MrWhite1878/AnalogEQ-Project/Simulation/Bell/bell.asc

C3: cap; 10n
C4: cap; 47n
R13: res; 2.2k
R14: res; 2.2k
R15: res; 4.7k
R16: res; 4.7k
R17: res; 12k
R18: res; 6.8k
R19: res; 6.8k
R20: res; 4.7k
R21: res; 4.7k
R22: res; 470
R23: res; 1k
R24: res; 12k
R25: res; {RV_23_4}
R26: res; {RV_12_4}
R27: res; {RV_12_6}
R28: res; {RV_23_6}
R29: res; {RV_12_7}
R30: res; {RV_23_7}
R31: res; {RV_12_7}
R32: res; {RV_23_7}
U5: TL072
U6: TL072
U7: TL072
U8: TL072
V1: voltage; ""; AC 1
V2: voltage; 18
V3: voltage; -18
Named nets: VS, 0, V+, V-, VM1
.ac oct 100 10 40k
.param Travel_4 = 0.2
.param R_Total_4 = 10k
.param TaperRatio_4 = table(Travel_4, 0,0, 0.1,0.05, 0.2,0.12, 0.3,0.22, 0.4,0.35, 0.5,0.5, 0.6,0.65, 0.7,0.78, 0.8,0.88, 0.9,0.95, 1,1)
.param RV_12_4 = {max(R_Total_4 * TaperRatio_4, 0.01 * R_Total_4)}
.param RV_23_4 = {max(R_Total_4 * (1 - TaperRatio_4), 0.01 * R_Total_4)}
.param Travel_6  = 0.5
.param R_Total_6 = 100k
.param TaperRatio_6 = table(Travel_6,  0,0, 0.1,0.05, 0.2,0.12, 0.3,0.22, 0.4,0.35, 0.5,0.5, 0.6,0.65, 0.7,0.78, 0.8,0.88, 0.9,0.95, 1,1)
.param RV_12_6 = {max(R_Total_6 * TaperRatio_6, 0.01 * R_Total_6)}
.param RV_23_6 = {max(R_Total_6 * (1 - TaperRatio_6), 0.01 * R_Total_6)}
.step param Travel_7 0 1 0.1
.param R_Total_7 = 100k
.param TaperRatio_7 = table(Travel_7, 0,0, 0.1,0.18, 0.2,0.38, 0.3,0.58, 0.4,0.74, 0.5,0.85, 0.6,0.92, 0.7,0.96, 0.8,0.98, 0.9,0.99, 1,1)
.param RV_12_7 = {max(R_Total_7 * TaperRatio_7, 0.01 * R_Total_7)}
.param RV_23_7 = {max(R_Total_7 * (1 - TaperRatio_7), 0.01 * R_Total_7)}
PTD902-2215K-B103
PTD904-2015K-C104
PTD902-1015K-B104
