MrWhite1878/AnalogEQ-Project/Simulation/Bell/douxchamps_bell.asc

V1: voltage; ""; AC 1
V2: voltage; 15
V3: voltage; -15
Named nets: VIN, 0, V+, V-
.ac oct 100 10 100k
.param posQ =0.5
.param posF =0.5
.step param posA list 0 0.25 0.75 1
