MrWhite1878/AnalogEQ-Project/Simulation/Bell/param_eq.asc

C1: cap; 1µf
C2: cap; 1nf
C3: cap; 1nf
R1: res; 10k
R2: res; 10k
R3: res; 10k
R4: res; 1k
R5: res; 15k
R6: res; 100k
R7: res; 11k
R8: res; 10k
R9: res; 1k
R10: res; 15k
R11: res; 3.9k
R12: res; 1k
R13: res; 21k
R14: res; 21k
R15: res; 1k
R16: res; 3.9k
R17: res; 22k
R18: res; 22k
R19: res; {RFV}
R20: res; {RFG}
R21: res; 390
R22: res; 12k
R23: res; 1k
R24: res; 9k
R25: res; 390
R26: res; 12k
U1: LT1358
U2: LT1358
U3: LT1358
U4: LT1358
U6: LT1358
V1: voltage; 10
V2: voltage; 10
V3: voltage; SINE(0 0.225); AC .225 0
Named nets: 0, out, input, Vneg, Vplus
RADJ 100k
RADJ
RADJ
RADJ
RADJ
.ac dec 1000 1 100000
RADJ 100k
GAIN?
Q
FREQ
.param RFV = (10k * posF + 10)
.param RFG = (10020 - RFV)
.step param posF list 0 0.5 0.9 1
