MrWhite1878/AnalogEQ-Project/Simulation/CombinedControl/combined.asc

C1: cap; 1µ
C2: cap; 1µ
C3: cap; 1µ
C4: cap; 10n
C5: cap; 680p
C6: cap; 10n
C7: cap; 100n
C8: cap; 100n
C9: cap; 15n
C10: cap; 15n
C11: cap; 10n
C12: cap; 47n
C13: cap; 1n
C14: cap; 4.7n
C15: cap; 47n
C16: cap; 47n
C17: cap; 47n
R1: res; 51k
R2: res; 3k
R3: res; 7.5k
R4: res; 1.2k
R5: res; 1.1k
R6: res; 3.9k
R7: res; 2.7k
R8: res; 1.8k
R9: res; 1.8k
R10: res; 12k
R11: res; 1k
R12: res; 1k
R13: res; 1k
R14: res; 2.2k
R15: res; 2.2k
R16: res; 4.7k
R17: res; 4.7k
R18: res; 12k
R19: res; 6.8k
R20: res; 6.8k
R21: res; 4.7k
R22: res; 4.7k
R23: res; 470
R24: res; 1k
R25: res; 12k
R26: res; 2.2k
R27: res; 2.2k
R28: res; 4.7k
R29: res; 4.7k
R30: res; 12k
R31: res; 6.8k
R32: res; 6.8k
R33: res; 4.7k
R34: res; 4.7k
R35: res; 470
R36: res; 1k
R37: res; 12k
R38: res; 47
R39: res; {RV_12_2}
R40: res; {RV_23_2}
R41: res; {RV_12_3}
R42: res; {RV_23_3}
R43: res; {RV_23_4}
R44: res; {RV_12_4}
R45: res; {RV_12_6}
R46: res; {RV_23_6}
R47: res; {RV_23_5}
R48: res; {RV_12_5}
R49: res; {RV_12_8}
R50: res; {RV_23_8}
R51: res; {RV_12_7}
R52: res; {RV_23_7}
R53: res; {RV_12_7}
R54: res; {RV_23_7}
R55: res; {RV_12_9}
R56: res; {RV_23_9}
R57: res; {RV_12_9}
R58: res; {RV_23_9}
R59: res; 139k
R60: res; 1k
R61: res; 12k
R62: res; 100
R63: res; 10k
R64: res; {RV_23_1}
R65: res; {RV_12_1}
R66: res; 47
R67: res; 220
U1: NE5532
U2: NE5532
U3: TL072
U4: TL072
U5: TL072
U6: TL072
U7: TL072
U8: TL072
U9: TL072
U10: TL072
U11: TL072
U12: TL072
U13: TL072
U14: TL072
V1: voltage; SINE(0 1.5 1k); AC 1
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
.param RV_12_1 = {max(R_Total_1 * TaperRatio_1, 0.01 * R_Total_1)}
.param RV_23_1 = {max(R_Total_1 * (1 - TaperRatio_1), 0.01 * R_Total_1)}
PTD902-2015K-A103
PTD902-2015K-A103
PTD902-1015K-B104
PTD902-1015K-B104
.dc oct V1 0.1 50 100
