MrWhite1878/AnalogEQ-Project/Simulation/Notch/notch.asc

C4: cap; 47n
C5: cap; 47n
C6: cap; 47n
R3: res; 139k
R7: res; 1k
R8: res; 12k
R9: res; 100
R10: res; 10k
R11: res; {RV_23_1}
R12: res; {RV_12_1}
U1: TL072
V1: voltage; ""; AC 1
V2: voltage; 18
V3: voltage; -18
Named nets: VLP, 0, V+, V-, VN
.ac oct 10000 100 500
.step param Travel_1 0 1 0.1
.param R_Total_1 = 10k
.param TaperRatio_1 = table(Travel_1, 0,0, 0.1,0.015, 0.2,0.035, 0.3,0.06, 0.4,0.10, 0.5,0.15, 0.6,0.24, 0.7,0.36, 0.8,0.54, 0.9,0.78, 1,1)
.param RV_12_1 = {max(R_Total_1 * TaperRatio_1, 0.01 * R_Total_1)}
.param RV_23_1 = {max(R_Total_1 * (1 - TaperRatio_1), 0.01 * R_Total_1)}
PTD902-2015K-A103
PTD902-2015K-A103
.noise V(vn) V1 oct 10000 10 40k
