MrWhite1878/AnalogEQ-Project/Simulation/Power/acac_doubler.asc

C1: cap; 470µ; Rser=0.1
C2: cap; 470µ; Rser=0.1
C3: cap; 100n
C4: cap; 100n
C5: cap; 100µ; Rser=0.1
C6: cap; 100µ; Rser=0.1
C7: cap; 470µ; Rser=0.1
C8: cap; 470µ; Rser=0.1
C9: cap; 470µ
C10: cap; 470µ
C11: cap; 100n
C12: cap; 100n
C13: cap; 100µ
C14: cap; 100µ
C15: cap; 1000µ
C16: cap; 1000µ
C17: cap; 100n
C18: cap; 100n
C19: cap; 100µ
C20: cap; 100µ
C21: cap; 1000µ
C22: cap; 1000µ
D1: diode; 1N4007
D2: diode; 1N4007
D3: diode; 1N4007
D4: diode; 1N4007
D5: diode; 1N4007
D6: diode; 1N4007
D7: diode; 1N4007
D8: diode; 1N4007
D9: diode; 1N4007
D10: diode; 1N4007
RL3: res; 175
RL4: res; 175
U1: LM7818
U2: LM7918
U3: LM7818
U4: LM7918
U5: LM7818
U6: LM7918
V1: voltage; SINE(0 17 55); Rser=2
V2: voltage; SINE(0 22.6 55)
V3: voltage; SINE(0 12.73 55); Rser=2
Named nets: V+, V-, 0, VIN, V+2, V-2, VIN2, V+3, V-3, VIN3
.tran 1
Expects 12VAC... make sure components voltage rating and wall wart output are compatible
Third Supply
