MrWhite1878/AnalogEQ-Project/Simulation/Power/Draft1.asc

I1: current; SINE(0 7.0710678 60)
L1: ind; 16; Rser=0
L2: ind; 1; Rser=0
R1: res; 60
R2: res; 20
R3: res; 40
K1 L1 L2 1
.tran 0.1666666666666
