MrWhite1878/AnalogEQ-Project/Simulation/Shelving/shelves.asc

C1: cap; 100n
C2: cap; 100n
C3: cap; 15n
C4: cap; 15n
R1: res; 1.8k
R2: res; 1.8k
R3: res; 12k
R4: res; 1k
R5: res; 1k
R6: res; 1k
R7: res; {RV_12_2}
R8: res; {RV_23_2}
R9: res; {RV_12_3}
R10: res; {RV_23_3}
U1: NE5532
V1: voltage; ""; AC 1
V2: voltage; 18
V3: voltage; -18
Named nets: VN, 0, V+, V-, VS
.ac oct 100 10 40k
PTD902-2215K-B103
PTD902-2215K-B103
.step param Travel_2 0 1 0.5
.param R_Total_2 = 10k
.param TaperRatio_2 = table(Travel_2, 0,0, 0.1,0.05, 0.2,0.12, 0.3,0.22, 0.4,0.35, 0.5,0.5, 0.6,0.65, 0.7,0.78, 0.8,0.88, 0.9,0.95, 1,1)
.param RV_12_2 = {max(R_Total_2 * TaperRatio_2, 0.01 * R_Total_2)}
.param RV_23_2 = {max(R_Total_2 * (1 - TaperRatio_2), 0.01 * R_Total_2)}
.step param Travel_3 0 1 0.5
.param R_Total_3 = 10k
.param TaperRatio_3 = table(Travel_3, 0,0, 0.1,0.05, 0.2,0.12, 0.3,0.22, 0.4,0.35, 0.5,0.5, 0.6,0.65, 0.7,0.78, 0.8,0.88, 0.9,0.95, 1,1)
.param RV_12_3 = {max(R_Total_3 * TaperRatio_3, 0.01 * R_Total_3)}
.param RV_23_3 = {max(R_Total_3 * (1 - TaperRatio_3), 0.01 * R_Total_3)}
.noise V(vs) V1 oct 100 10 40k
