MrWhite1878/AnalogEQ-Project/Simulation/Power/pifilter.asc

C1: cap; 10µ; Rser=1
C2: cap; 10µ; Rser=1
C3: cap; 10µ; Rser=1
C4: cap; 10µ; Rser=1
L1: ind; 10µ; Rser=1
L2: ind; 10µ; Rser=1
V1: voltage; SINE(15 50m 100k); AC 1
V2: voltage; SINE(-15 50m 100k); AC 1
Named nets: VOUT+, VOUT-, 0
.tran 100u
.ac dec 100 1 1Meg
ferrite bead inductors
