MrWhite1878/AnalogEQ-Project/sim/CombinedControl/combined.asc

C1: cap; 1µ
C2: cap; 1µ
C3: cap; 1µ
C4: cap; 10n
C5: cap; 680p
C6: cap; 10n
C7: cap; 100n
C8: cap; 100n
C9: cap; 15n
C10: cap; 15n
C11: cap; 10n
C12: cap; 47n
C13: cap; 1n
C14: cap; 4.7n
C15: cap; 220n
C16: cap; 220n
C17: cap; 220n
R1: res; 51k
R2: res; 3k
R3: res; 7.5k
R4: res; 1.2k
R5: res; 1.1k
R6: res; 3.9k
R7: res; 2.7k
R8: res; 1.8k
R9: res; 1.8k
R10: res; 12k
R11: res; 1k
R12: res; 1k
R13: res; 1k
R14: res; 2.2k
R15: res; 2.2k
R16: res; 4.7k
R17: res; 4.7k
R18: res; 12k
R19: res; 6.8k
R20: res; 6.8k
R21: res; 4.7k
R22: res; 4.7k
R23: res; 470
R24: res; 1k
R25: res; 12k
R26: res; 2.2k
R27: res; 2.2k
R28: res; 4.7k
R29: res; 4.7k
R30: res; 12k
R31: res; 6.8k
R32: res; 6.8k
R33: res; 4.7k
R34: res; 4.7k
R35: res; 470
R36: res; 1k
R37: res; 12k
R38: res; 100k
R39: res; 39k
R40: res; 1k
R41: res; 12k
R42: res; 100
R43: res; 10k
RG1: res; {10k*(1-posb)+20}
RG2: res; {10k*(1-post)+20}
RG3: res; {100k*(1-posF)+20}
RG4: res; {100k*(1-posF)+20}
RG5: res; {100k*(1-posQ)+20}
RG6: res; {10k*(1-posA)+20}
RG7: res; {100k*(1-posF)+20}
RG8: res; {100k*(1-posF)+20}
RG9: res; {100k*(1-posQ)+20}
RG10: res; {10k*(1-posA)+20}
RG11: res; {10k*(1-posF)+20}
RV1: res; {10k*posb+20}
RV2: res; {10k*post+20}
RV3: res; {100k*posF+20}
RV4: res; {100k*posF+20}
RV5: res; {100k*posQ+20}
RV6: res; {10k*posA+20}
RV7: res; {100k*posF+20}
RV8: res; {100k*posF+20}
RV9: res; {100k*posQ+20}
RV10: res; {10k*posA+20}
RV11: res; {10k*posF+20}
U1: NE5532
U2: NE5532
U3: NE5532
U4: TL072
U5: TL072
U6: TL072
U7: TL072
U8: TL072
U9: TL072
U10: TL072
U11: TL072
U12: NE5532
V1: voltage; ""; AC 1
V2: voltage; 15
V3: voltage; -15
Named nets: V+, V-, 0, VIN, VLP, VHP, VN, VS, VM1, VM2
.ac oct 100 2 200kHz
inverted
.param posb = 0.4
.param post = 0.4
.param posF = 0.25
.param posQ = 0.5
.param posA = 0.75
another set of params
noninverted
parameters
.tran 10m
.noise V(VM2) V1 oct 100 2 200k
