MrWhite1878/AnalogEQ-Project/Simulation/HPF/hpf.asc

C1: cap; 1µ
C2: cap; 1µ
C3: cap; 1µ
C4: cap; 1µ
C5: cap; 1µ
C6: cap; 1µ
C7: cap; 1µ
C8: cap; 1µ
C9: cap; 1µ
R1: res; 15k
R2: res; 7.5k
R3: res; 27k
R4: res; 3.9k
R5: res; 11k
R6: res; 10k
R7: res; 51k
R8: res; 3k
R9: res; 7.5k
U1: NE5532
U2: TL072
U3: TL072
U4: TL072
V1: voltage; ""; AC 1
V2: voltage; 15
V3: voltage; -15
Named nets: VIN, 0, V+, V-, VOUT, VOUT3, VOUT2
.ac oct 100 1u 10G
.ac oct 100 1 40
