MrWhite1878/AnalogEQ-Project/Simulation/LPF/lpf_real.asc

C1: cap; 11.1n
C2: cap; 28.2n
C3: cap; 1.61n
C4: cap; 10n
C5: cap; 680p
C6: cap; 10n
R1: res; 1k
R2: res; 1k
R3: res; 1k
R4: res; 1.2k
R5: res; 1.1k
R6: res; 3.9k
R7: res; 2.7k
U1: NE5532
U2: NE5532
V4: voltage; ""; AC 1
V5: voltage; 15
V6: voltage; -15
Named nets: VIN, 0, V+, V-, VOUT1, VOUT2
.ac oct 100 1u 10G
.ac oct 100 1k 10k
